techy-robot/JoyKey/media/Dial View.png

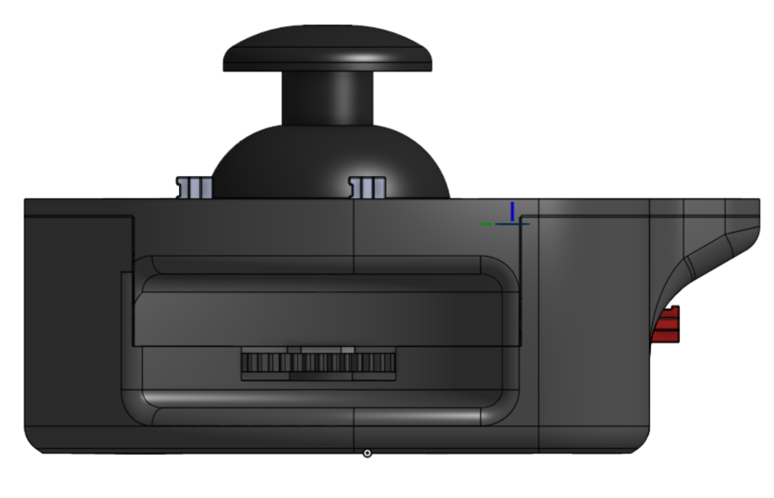
media/Dial View.png
