techy-robot/JoyKey/mounting style reference.webp

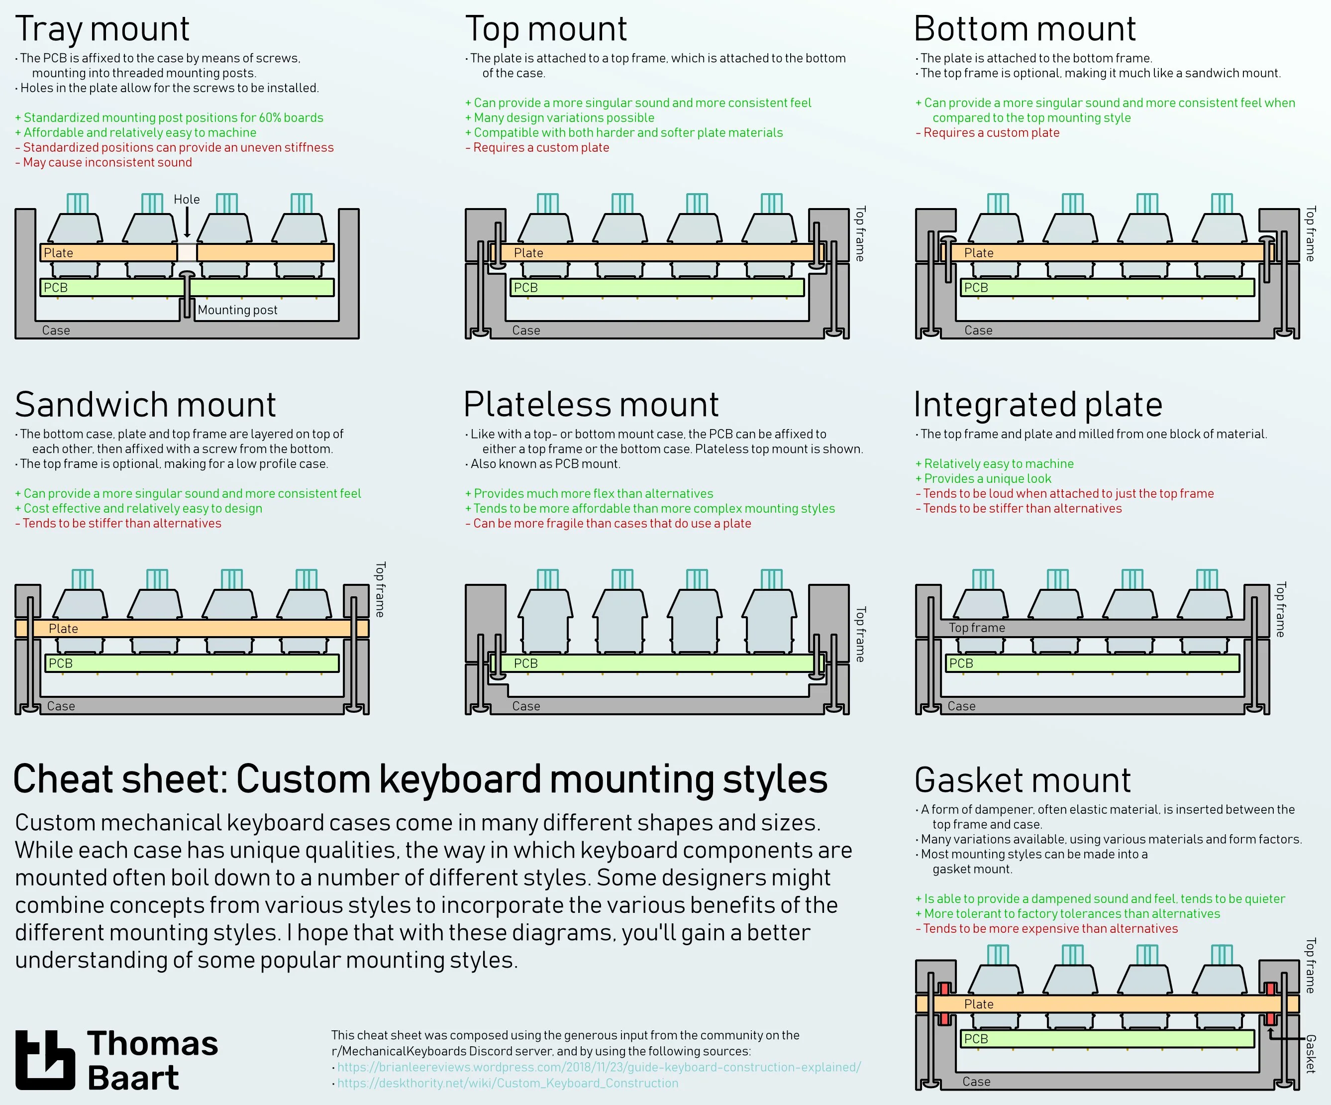
mounting style reference.webp
