techy-robot/JoyKey/firmware/QMK/rp2040_xaio/rp2040_xaio.h

#pragma once
#include "utils/encoder_handler.h"
#include "print.h"

#include "qp.h"
#include "qp_comms.h"
#include "qp_sh1106_opcodes.h"

#include "color.h"
#include "config.h"

#include "media/fonts/thintel15.qff.h"

#include "utils/settings.h"
#include "dynamic_keymap.h"
#include "utils/keyname_map.h"

extern painter_device_t oled;
extern painter_font_handle_t default_font;

extern bool update_oled;

void keyboard_post_init_kb(void);

bool process_record_kb(uint16_t keycode, keyrecord_t *record);
